bitfixer/bf-romulator/tools/dgrom.cpp

// z80program.h
// This is a modified version of the digital group ZE Audio ROM, which was used for 
// loading software from cassette.
// I modified the 'read byte' subroutine to read bytes from a binary file instead of
// from the comparator on the dg's cassette port.
// Michael Hill
// bitfixer@bitfixer.com

#include <stdio.h>
#include <string.h>
#include <stdint.h>

unsigned char program[] = 
{
0xc3, // 0 (0)
0x33, // 1 (1)
0x0, // 2 (2)
0xd2, // 3 (3)
0xe5, // 4 (4)
0xe1, // 5 (5)
0xe4, // 6 (6)
0xa0, // 7 (7)
0xc3, // 8 (10)
0x2, // 9 (11)
0x1, // a (12)
0xda, // b (13)
0xad, // c (14)
0xb8, // d (15)
0xb0, // e (16)
0xa0, // f (17)
0xc3, // 10 (20)
0x5, // 11 (21)
0x1, // 12 (22)
0xc9, // 13 (23)
0xce, // 14 (24)
0xc9, // 15 (25)
0xd4, // 16 (26)
0xc9, // 17 (27)
0xc3, // 18 (30)
0x8, // 19 (31)
0x1, // 1a (32)
0xc1, // 1b (33)
0xcc, // 1c (34)
0xc9, // 1d (35)
0xda, // 1e (36)
0xc5, // 1f (37)
0xc3, // 20 (40)
0xb, // 21 (41)
0x1, // 22 (42)
0xa0, // 23 (43)
0xc3, // 24 (44)
0xe1, // 25 (45)
0xf3, // 26 (46)
0xf3, // 27 (47)
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

0xcd, // 7b (173)
0x9c, // 7c (174)
0x0, // 7d (175)
0x6, // 7e (176)
0x80, // 7f (177)
0x10, // 80 (200)
0xfe, // 81 (201)
0x12, // 82 (202)
0x1a, // 83 (203)
0xbc, // 84 (204)
0x7a, // 85 (205)
0x28, // 86 (206)
0x2, // 87 (207)
0x3e, // 88 (210)
0xae, // 89 (211)
0xe6, // 8a (212)
0x7, // 8b (213)
0xf6, // 8c (214)
0xb0, // 8d (215)
0xcd, // 8e (216)
0xfa, // 8f (217)
0x0, // 90 (220)
0x2a, // 91 (221)
0x1a, // 92 (222)
0x1, // 93 (223)
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
    fwrite(program, 1, program_bytes, fp);
    fclose(fp);

    const char* message = "ROMULATOR";
    for (int i = 0; i < strlen(message); i++)
    {
        char c = message[i];
        uint8_t cc = 193 + (c - 'A');
        printf("%d: %X %o\n", c, cc, cc);
    }
}
