bitfixer/bf-romulator/tools/libRomulatorDebug.h

#ifndef __LIB_ROMULATOR_DEBUG__
#define __LIB_ROMULATOR_DEBUG__

#include <stdint.h>

void romulatorInit();
void romulatorClose();

bool romulatorReadMemory(uint8_t* buffer, int retries);
void romulatorWriteMemory(uint8_t* send_buffer, bool verify);
bool romulatorReadVram(uint8_t* vram, int size, int valid_bytes, int retries);
void romulatorWriteConfig(int configSetting);
uint8_t romulatorReadConfig();
void romulatorHaltCpu();
void romulatorStartCpu();


#endif
